dezanche/32-channel_RF_system/Photos/IMG_20170829_212727.jpg

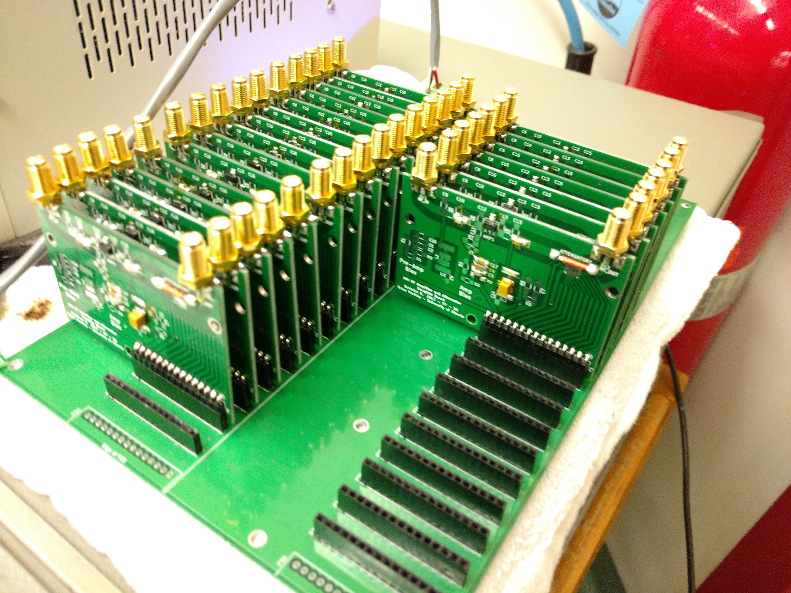
Photos/IMG_20170829_212727.jpg
