dezanche/32-channel_RF_system/Photos/IMG_20170831_181111.jpg

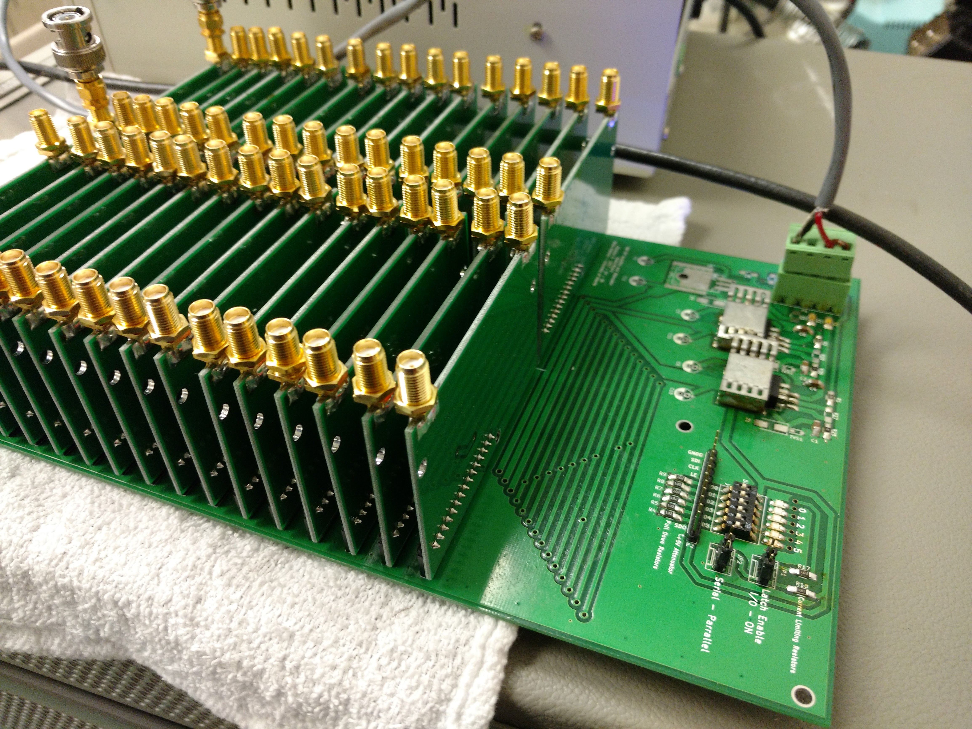
Photos/IMG_20170831_181111.jpg
