dezanche/32-channel_RF_system/Motherboard/pdf/MRI-RF-Amplifier-F.SilkS.pdf

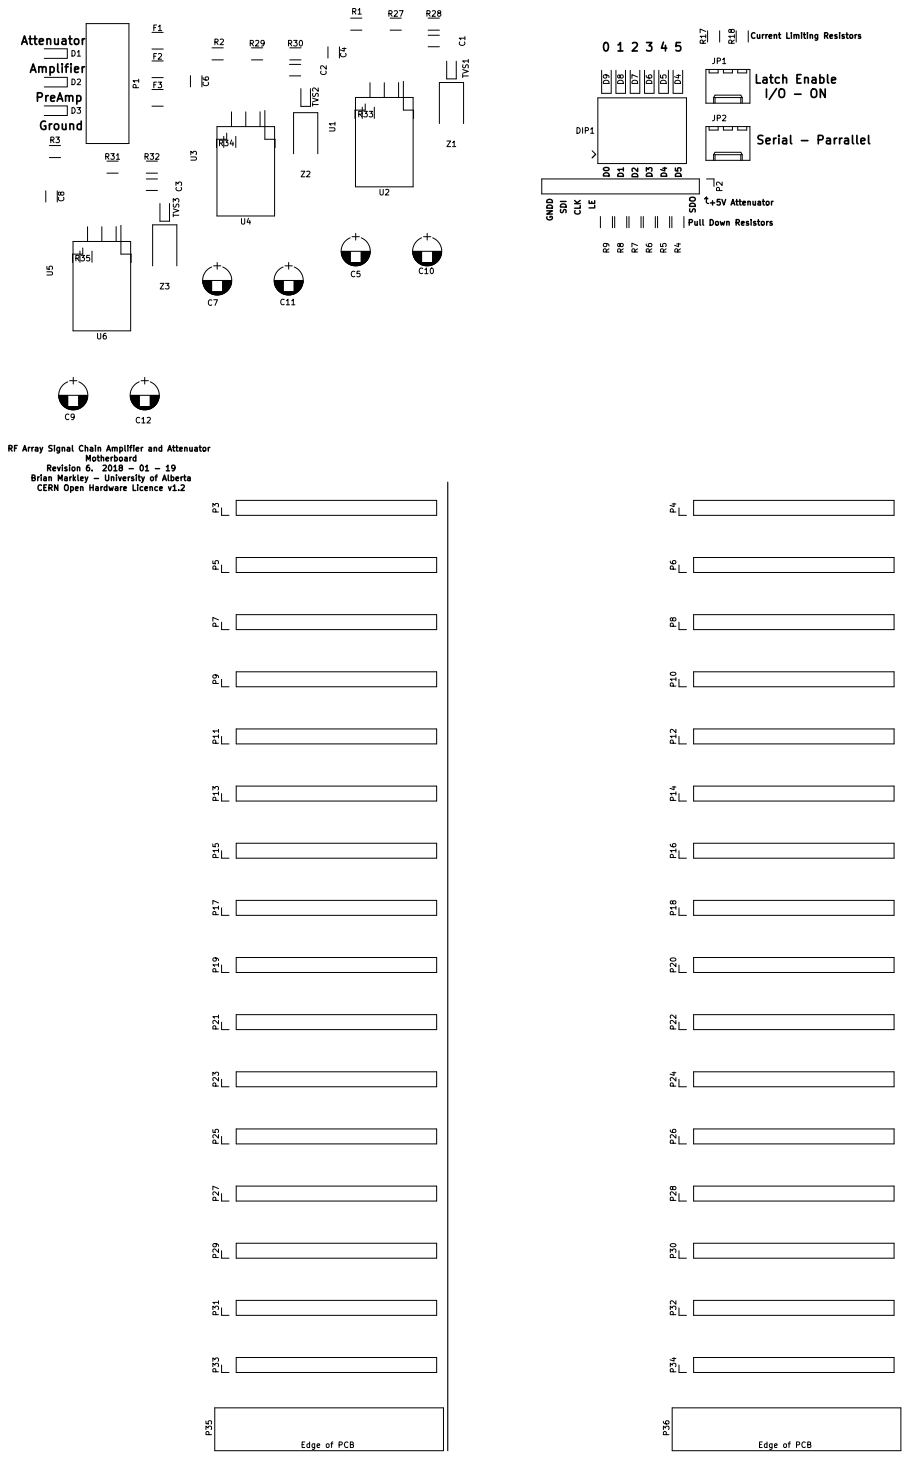
[picture p16: page 1]

I/O - ON Ground Attenuator Amplifier
