dezanche/32-channel_RF_system/Motherboard/pdf/MRI-RF-Amplifier.pdf

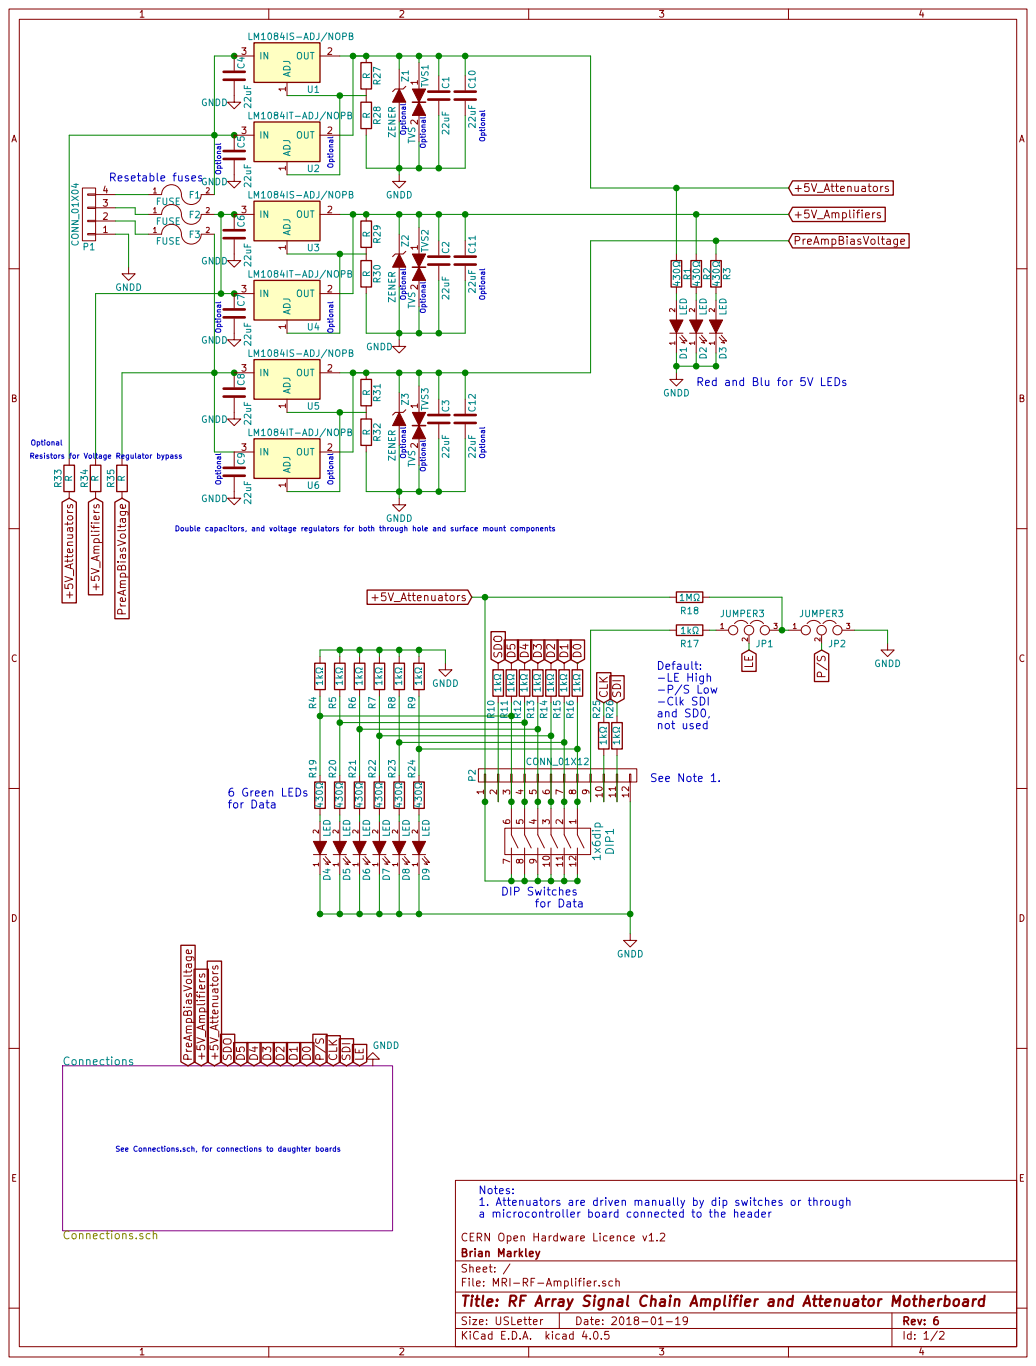
[picture p17: page 1]

1 2 TVS1 TVS Z1 ZENER C1 22uF 430 R2 430 R3 R19 430 R10 1k R20 430 R21 430 R22 430 R23 430 R24 430 Red and Blu for 5V LEDs R11 1k R12 1k R13 1k R14 1k R15 1k R25 1k R26 1k R16 1k R18

Notes: 1. Attenuators are driven manually by dip switches or through
a microcontroller board connected to the header
CERN Open Hardware Licence v1.2
File: MRI-RF-Amplifier.sch Sheet: / Brian Markley

Id: 1/2 Title: RF Array Signal Chain Amplifier and Attenuator Motherboard

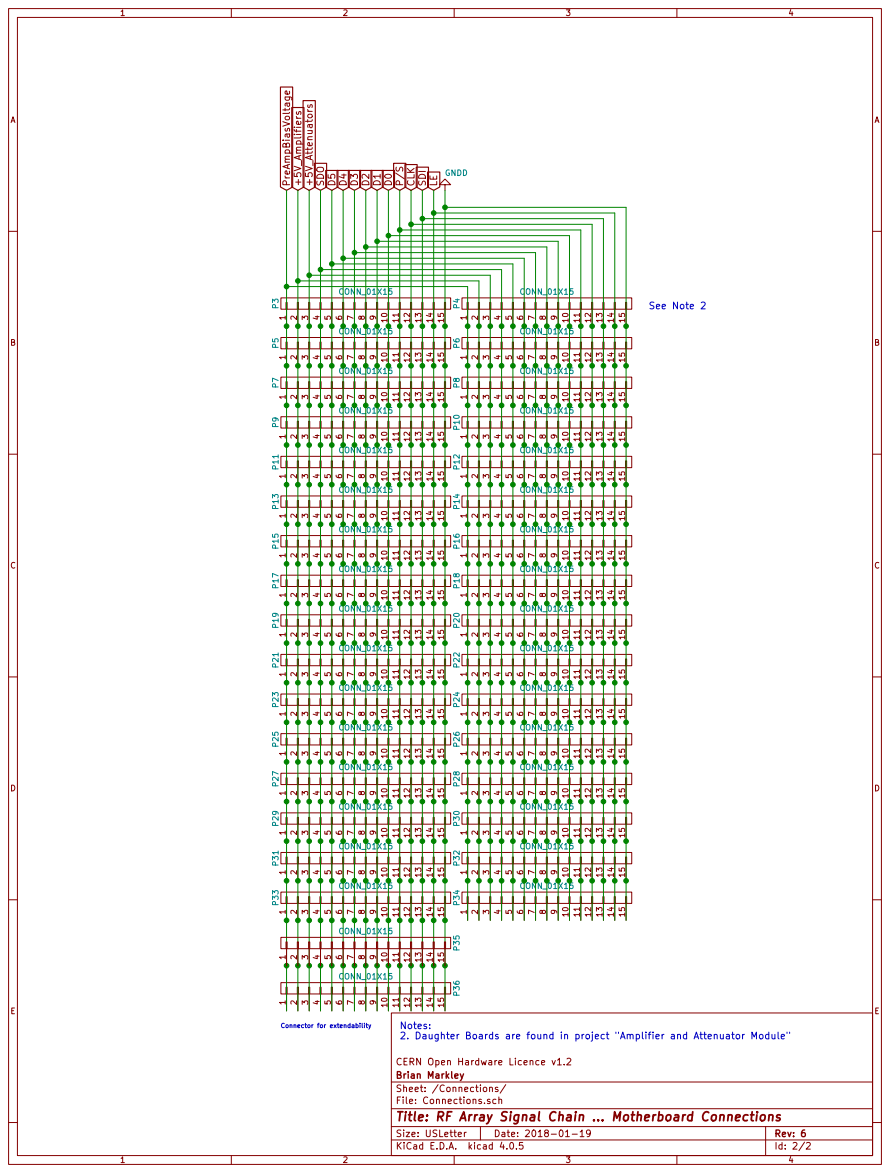
[picture p18: page 2]

File: Connections.sch Sheet: /Connections/ Brian Markley

Id: 2/2 Title: RF Array Signal Chain ... Motherboard Connections
