dezanche/32-channel_RF_system/Amplifier and Attenuator Module/Pdf/Amplifier and Attenuator Module-F.SilkS.pdf

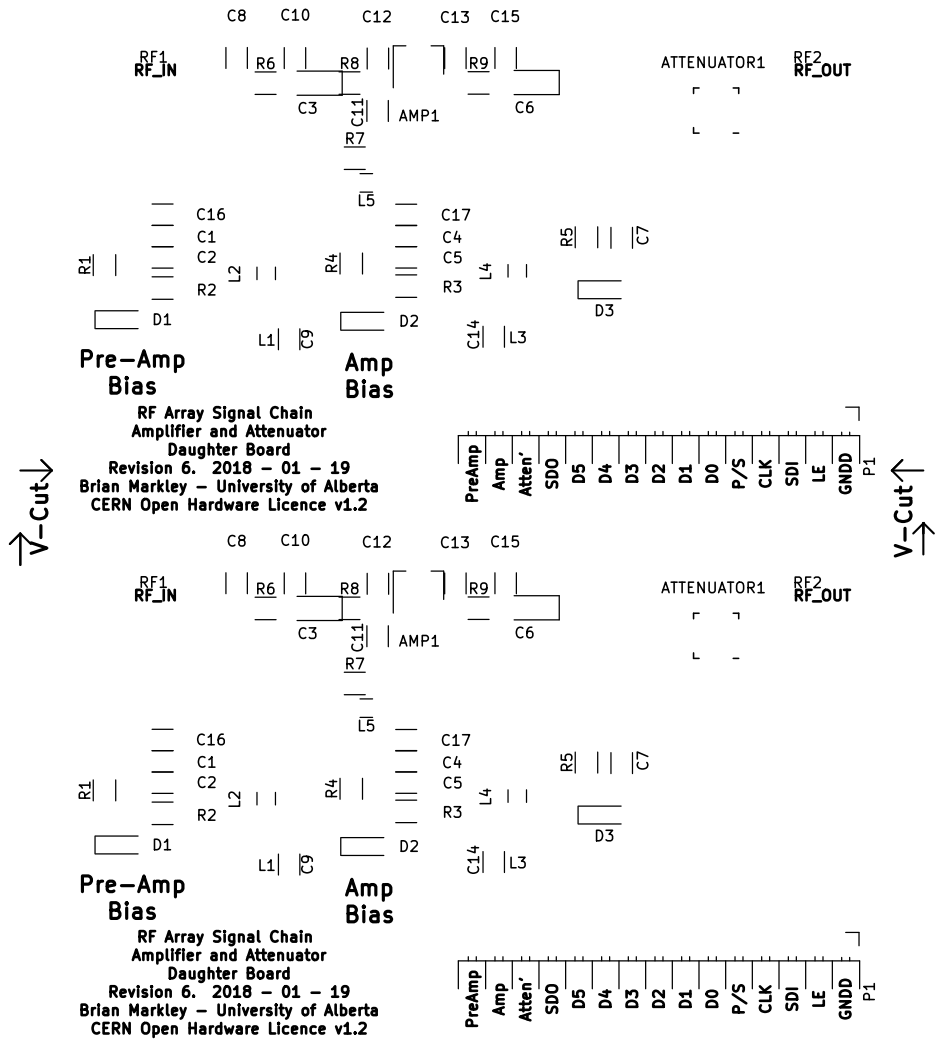
[picture p19: page 1]

Pre-Amp Bias
RF Array Signal Chain Amplifier and Attenuator Daughter Board Revision 6. 2018 - 01 - 19 Brian Markley - University of Alberta CERN Open Hardware Licence v1.2Amp Bias
