dezanche/32-channel_RF_system/Amplifier and Attenuator Module/Pdf/Amplifier and Attenuator Module.pdf

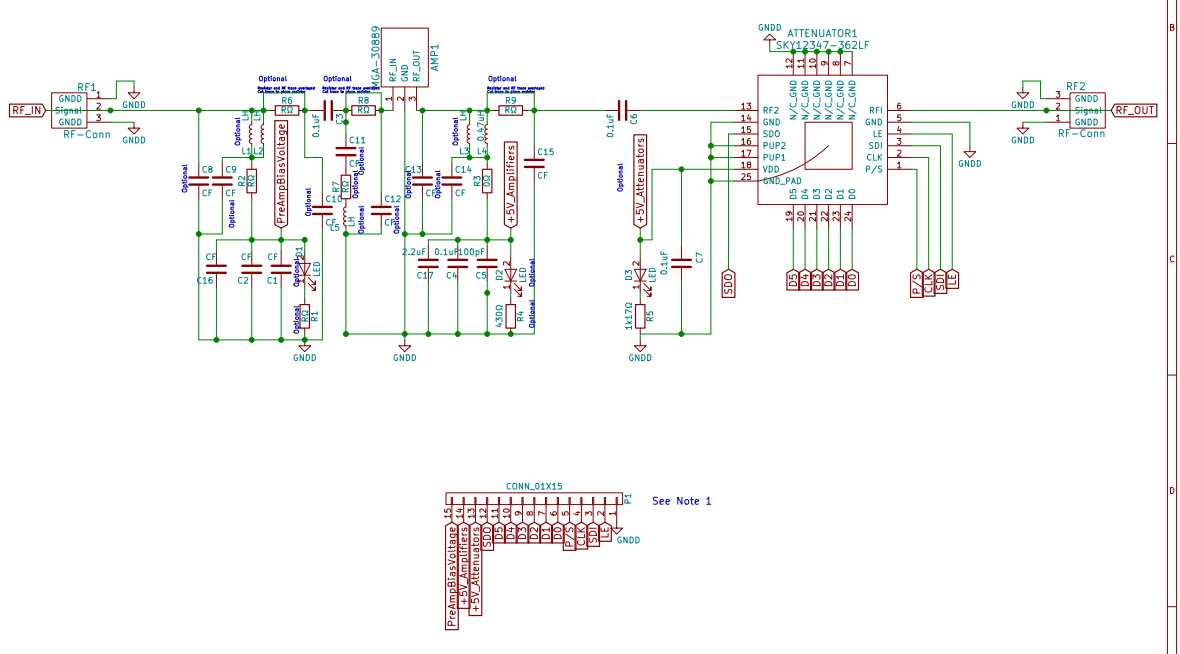
[picture p20: page 1]

CERN Open Hardware Licence v1.2 RF_IN
L5 LH R7R C11 CFR8R

3 AMP1 MGA-30889 GNDD C6 0.1uFC3 0.1uF +5V_Amplifiers P/S 1 CLK 2 SDI 3

Resistor and RF trace overlayed Cut trace to place resistor C14 CF R6R

Notes: 1: See project titled "MRI-RF-Amplifier.pro" in folder "Motherboard" for the PCB which

File: Amplifier and Attenuator Module.sch Sheet: / Brian Markley

Id: 1/1 Title: RF Array Signal Chain Amplifier and Attenuator Daughter Board
