dezanche/32-channel_RF_system/Motherboard/pdf/MRI-RF-Amplifier-F.Mask.pdf

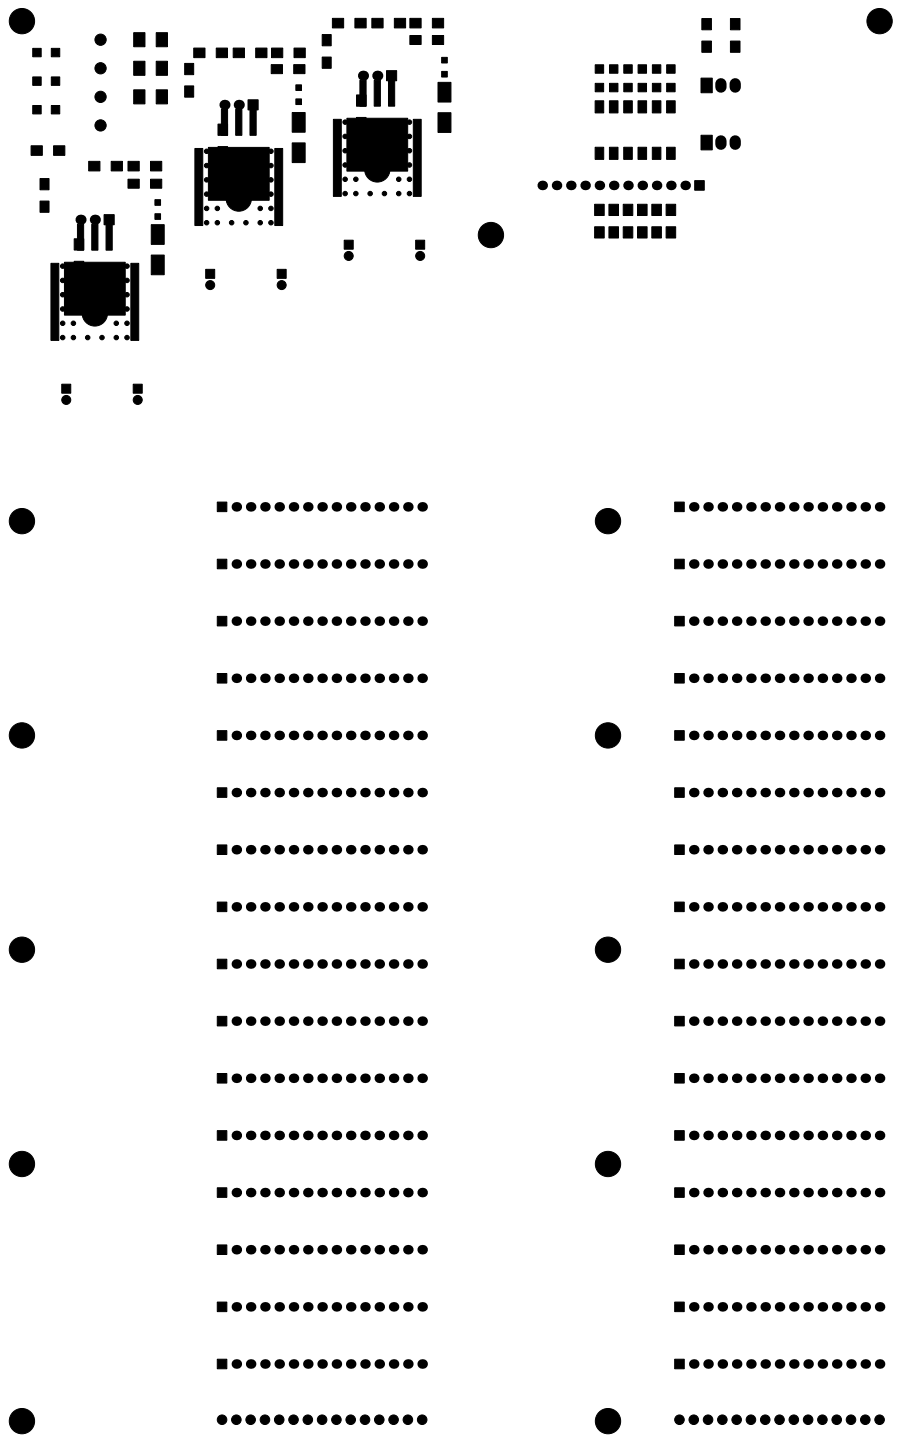
[picture p24: page 1]
