dezanche/32-channel_RF_system/Amplifier and Attenuator Module/Pdf/Amplifier and Attenuator Module-B.Cu.pdf

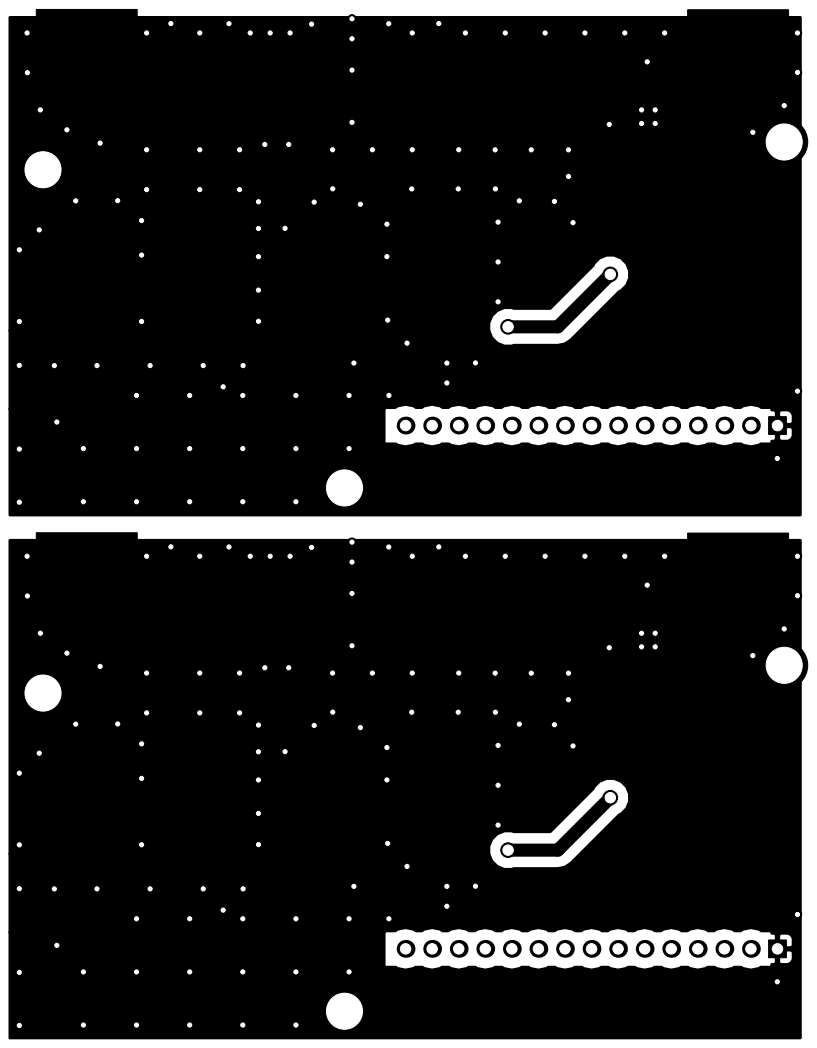
[picture p25: page 1]
