dezanche/32-channel_RF_system/Amplifier and Attenuator Module/Pdf/Amplifier and Attenuator Module-B.Mask.pdf

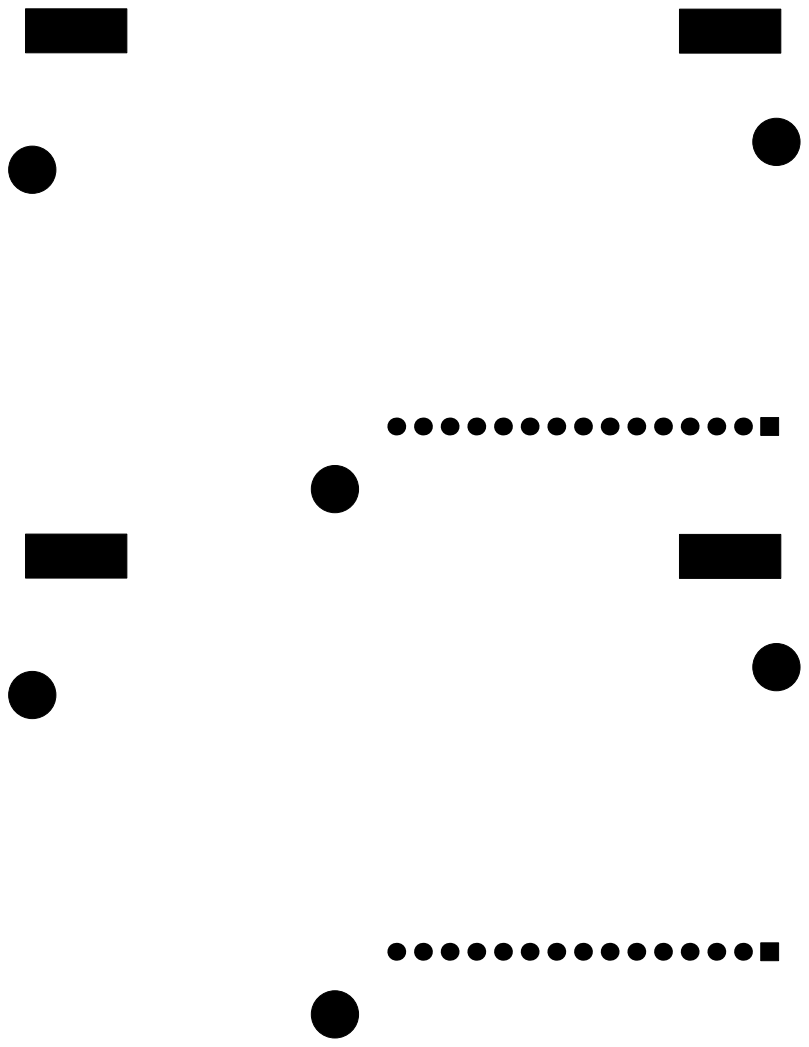
[picture p26: page 1]
