dezanche/32-channel_RF_system/Amplifier and Attenuator Module/Pdf/Amplifier and Attenuator Module-F.Cu.pdf

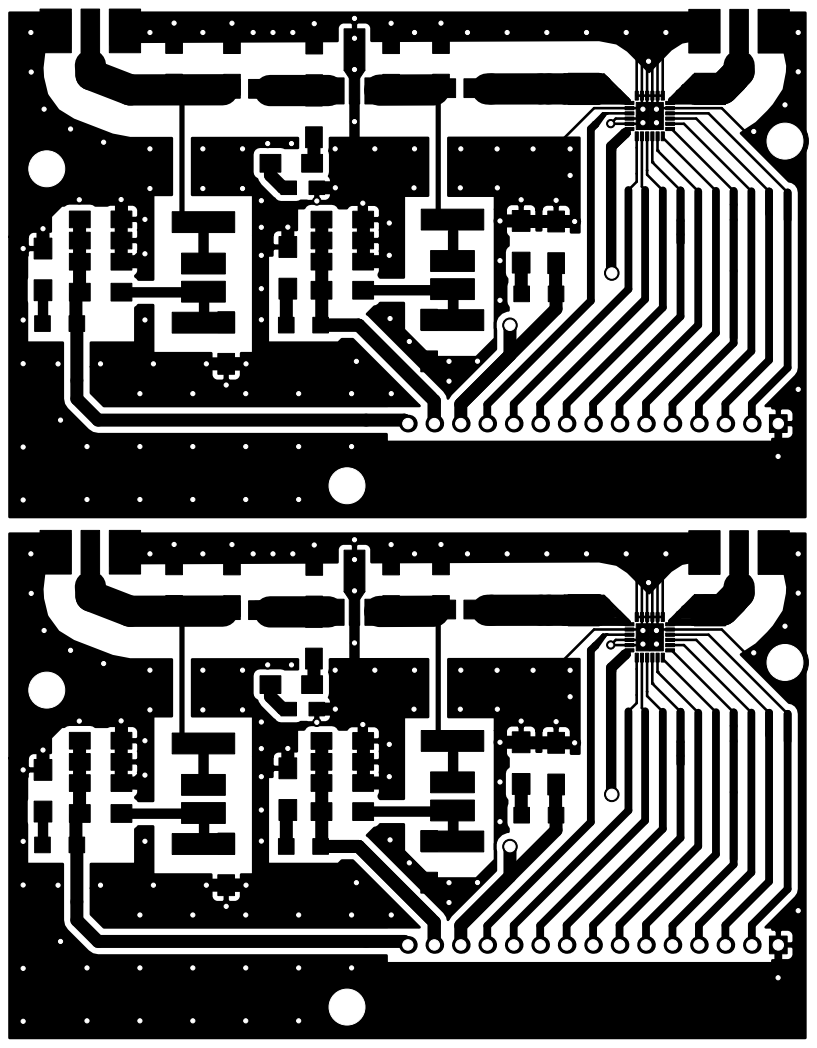
[picture p27: page 1]
