dezanche/32-channel_RF_system/Amplifier and Attenuator Module/Pdf/Amplifier and Attenuator Module-F.Mask.pdf

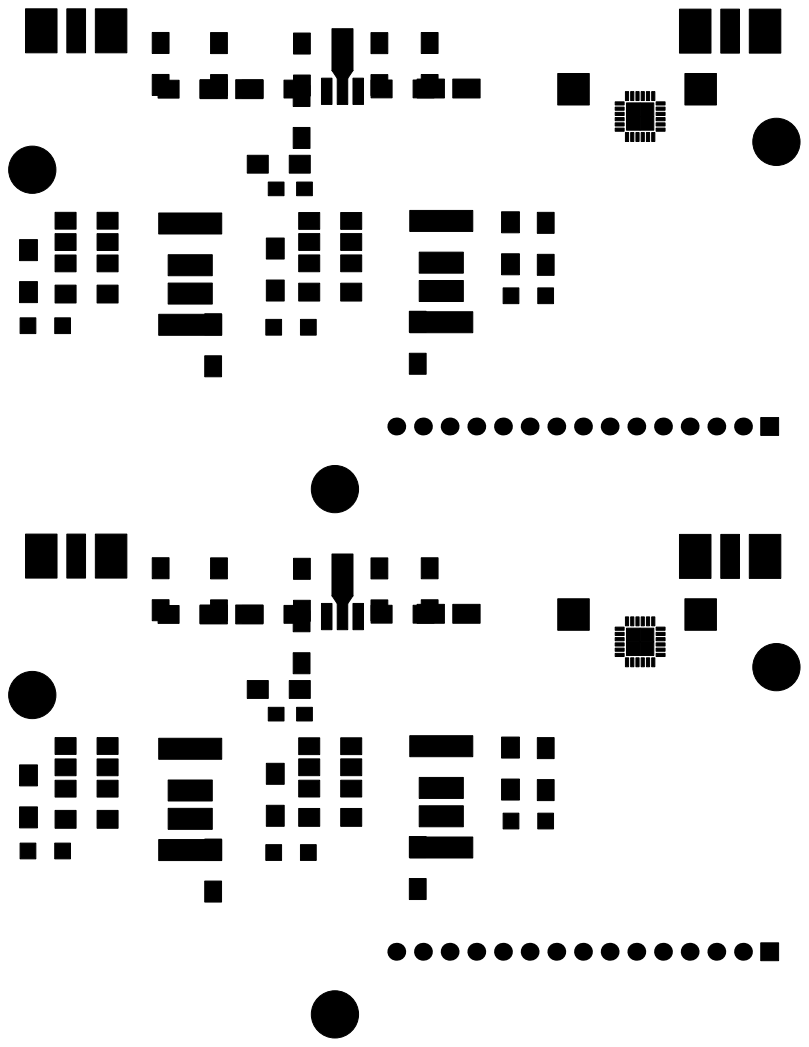
[picture p28: page 1]
